alexiamihai/TSC---ebookReader/Images/Screenshot 2025-04-05 202603.png

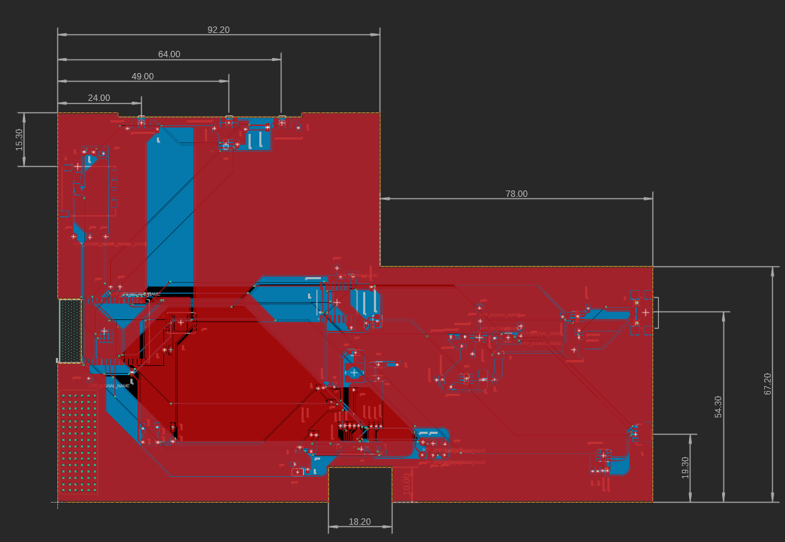
Images/Screenshot 2025-04-05 202603.png
