alexiamihai/TSC---ebookReader/Images/Screenshot 2025-04-05 202728.png

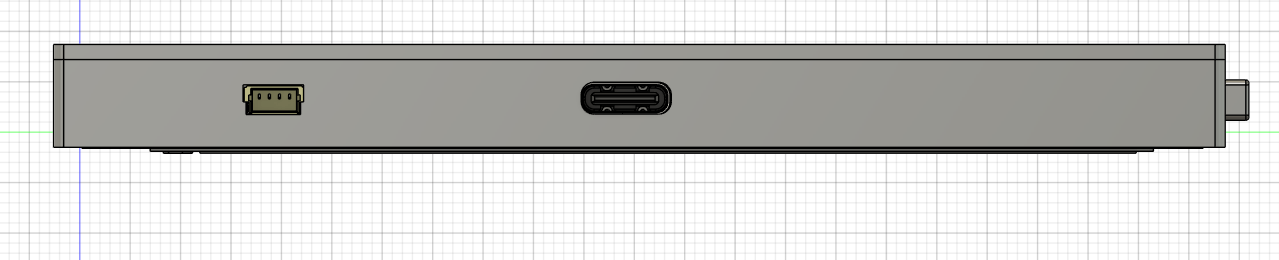
Images/Screenshot 2025-04-05 202728.png
